William-Dorsch/Open-Source-Train-SIm-Controller-v2/3d files/throttle assembly/throttleHousing.stl

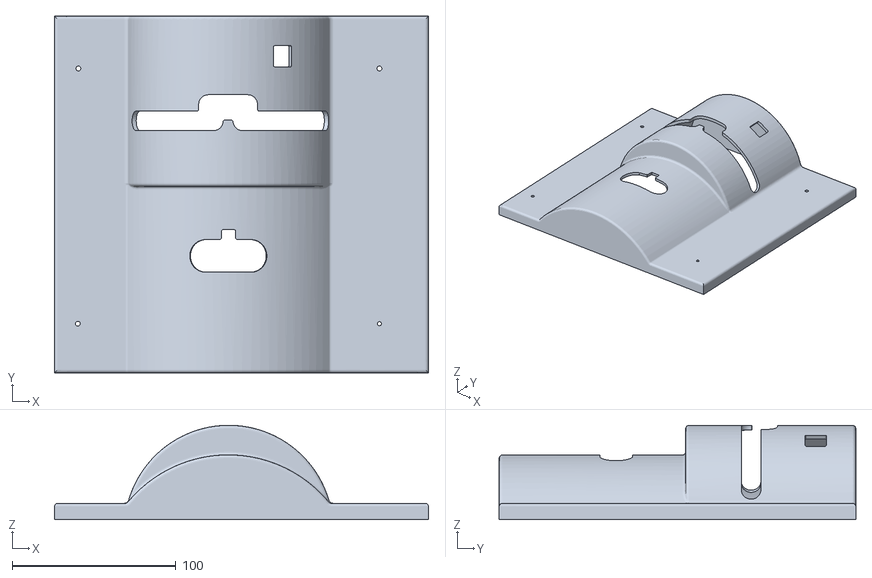
[picture p15: CAD file, 2025-07-15]
3d files/throttle assembly/throttleHousing.stl
228.6 x 218.0 x 57.7
