William-Dorsch/Open-Source-Train-SIm-Controller-v2/3d files/brake assembly/automatic brake/automaticBrakeHandleShaft.stl

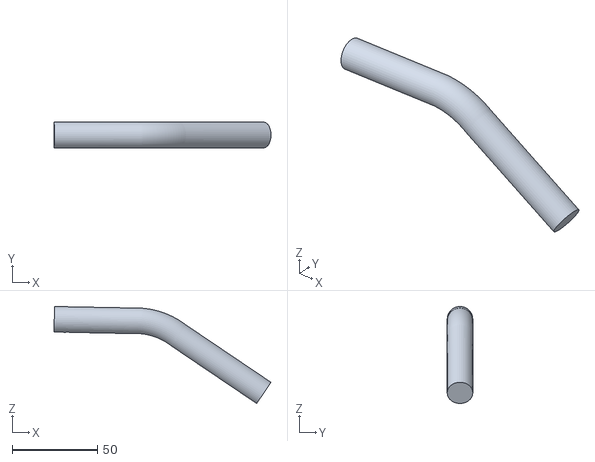
[picture p17: CAD file, 2025-07-15]
3d files/brake assembly/automatic brake/automaticBrakeHandleShaft.stl
127.0 x 15.0 x 56.8
