William-Dorsch/Open-Source-Train-SIm-Controller-v2/3d files/brake assembly/independent brake/independentBrakeHandleShaft.stl

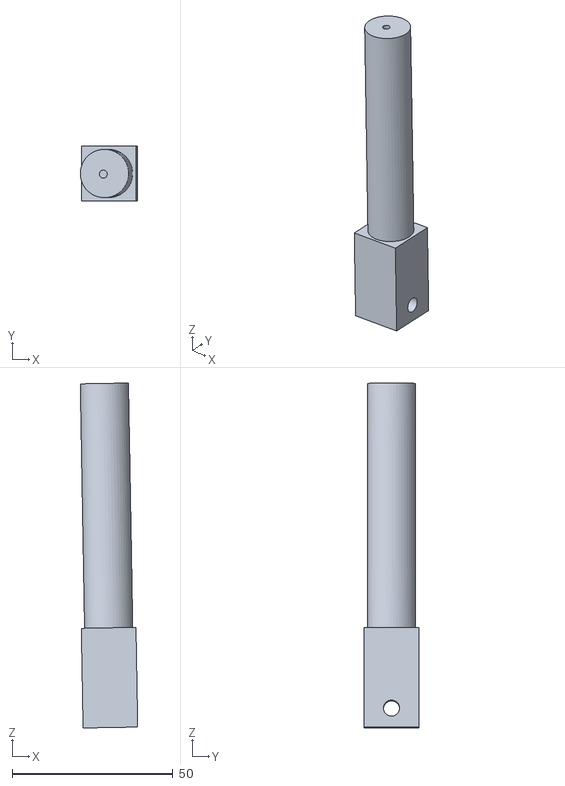
[picture p18: CAD file, 2025-07-15]
3d files/brake assembly/independent brake/independentBrakeHandleShaft.stl
17.9 x 17.0 x 107.3
