William-Dorsch/Open-Source-Train-SIm-Controller-v2/3d files/buttons/hornButtonHousing.stl

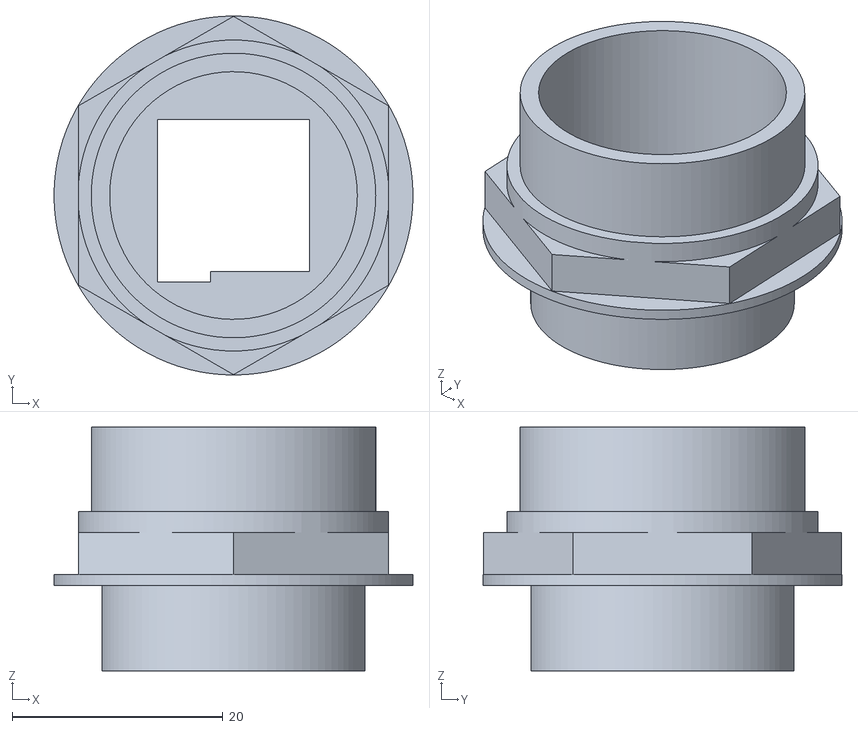
[picture p19: CAD file, 2026-01-03]
3d files/buttons/hornButtonHousing.stl
34.1 x 34.1 x 23.1
