William-Dorsch/Open-Source-Train-SIm-Controller-v2/3d files/throttle assembly/reverser/1x potentiometerHolderShort.stl

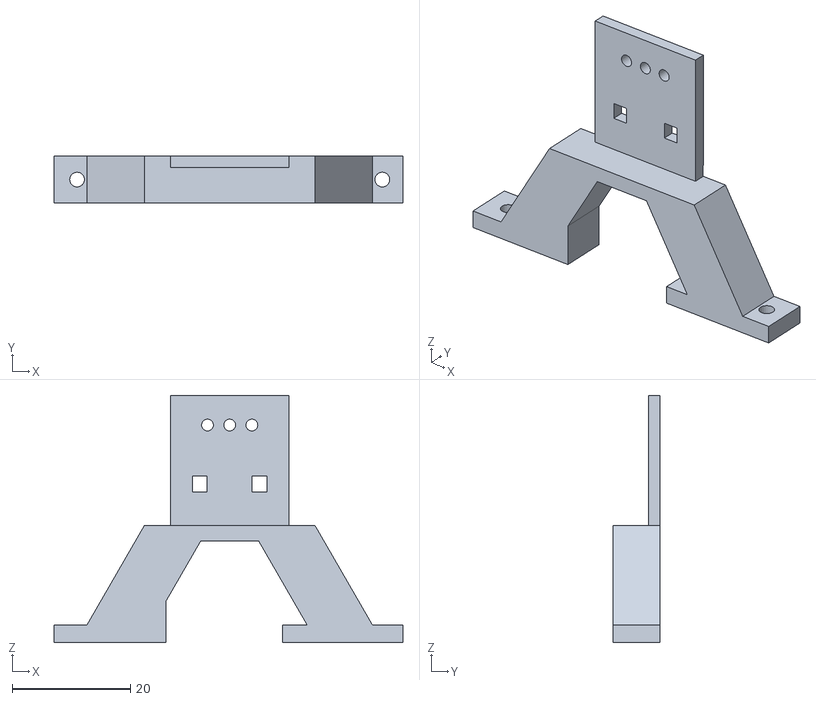
[picture p20: CAD file, 2025-07-15]
3d files/throttle assembly/reverser/1x potentiometerHolderShort.stl
59.0 x 8.00 x 41.8
