William-Dorsch/Open-Source-Train-SIm-Controller-v2/3d files/throttle assembly/throttle/throttleHandle.stl

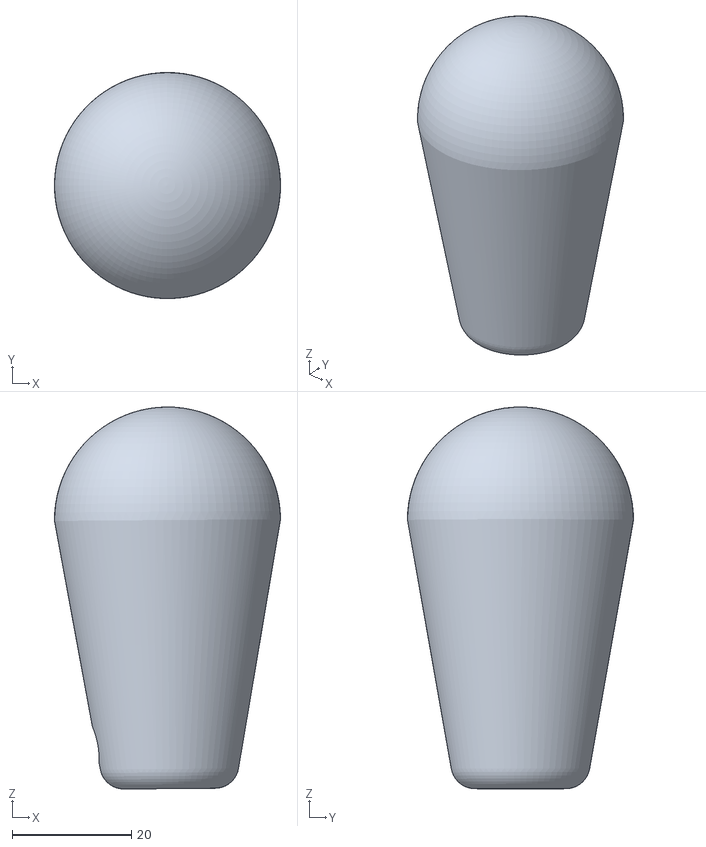
[picture p21: CAD file, 2025-07-15]
3d files/throttle assembly/throttle/throttleHandle.stl
37.9 x 37.9 x 64.0
