William-Dorsch/Open-Source-Train-SIm-Controller-v2/3d files/brake assembly/30A-CDW frame.stl

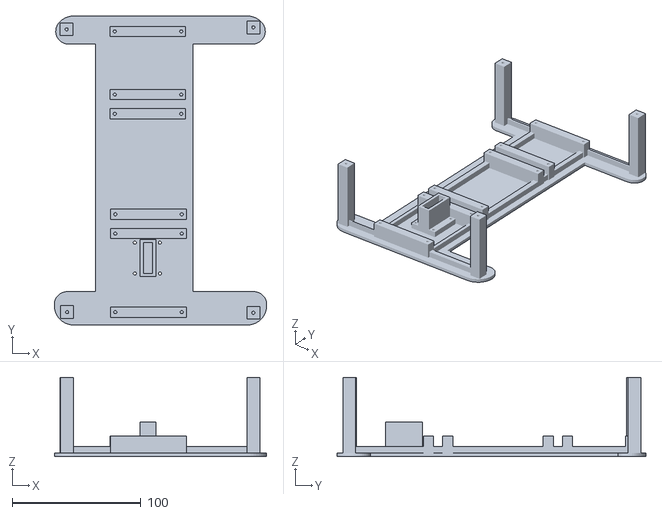
[picture p22: CAD file, 2025-07-15]
3d files/brake assembly/30A-CDW frame.stl
165.0 x 240.0 x 61.7
