William-Dorsch/Open-Source-Train-SIm-Controller-v2/3d files/brake assembly/automatic brake/automaticBrakeAxle.stl

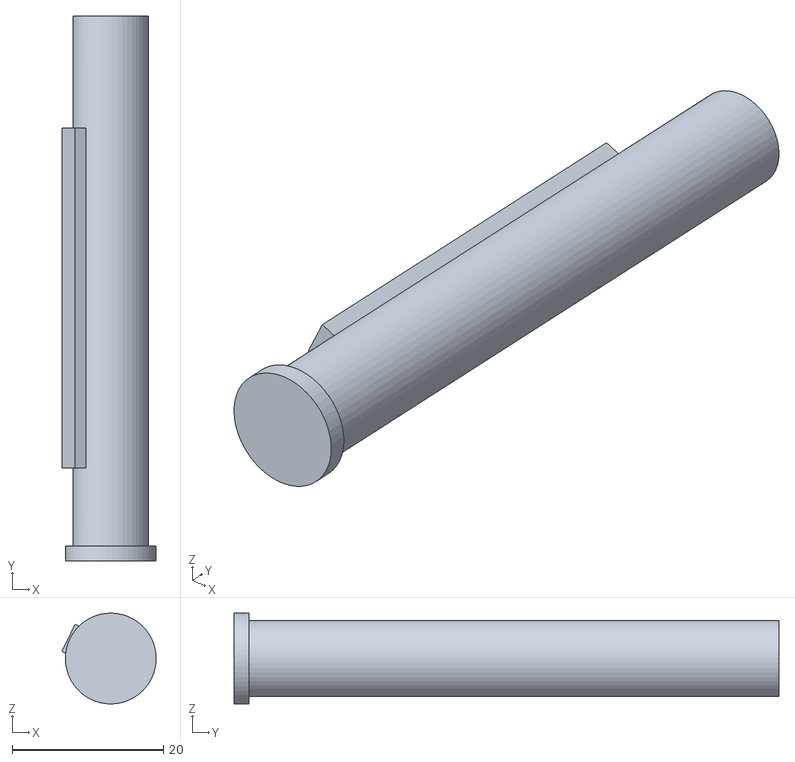
[picture p23: CAD file, 2025-07-15]
3d files/brake assembly/automatic brake/automaticBrakeAxle.stl
12.5 x 72.0 x 12.0
