William-Dorsch/Open-Source-Train-SIm-Controller-v2/3d files/brake assembly/independent brake/independentBrakeAxle.stl

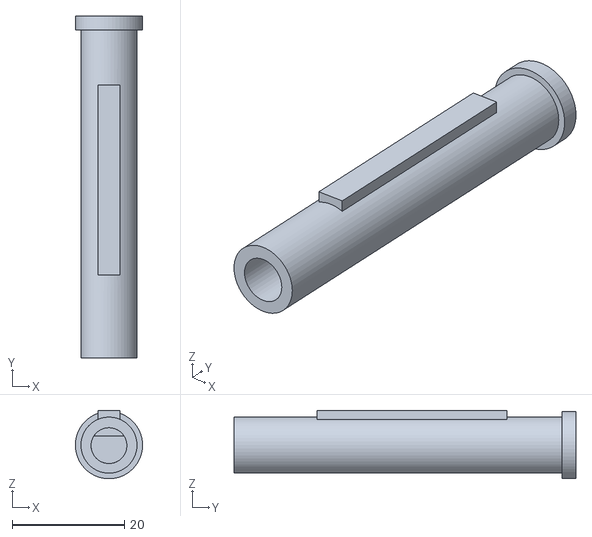
[picture p24: CAD file, 2025-07-15]
3d files/brake assembly/independent brake/independentBrakeAxle.stl
12.0 x 61.0 x 12.2
