William-Dorsch/Open-Source-Train-SIm-Controller-v2/3d files/buttons/sandbutton.stl

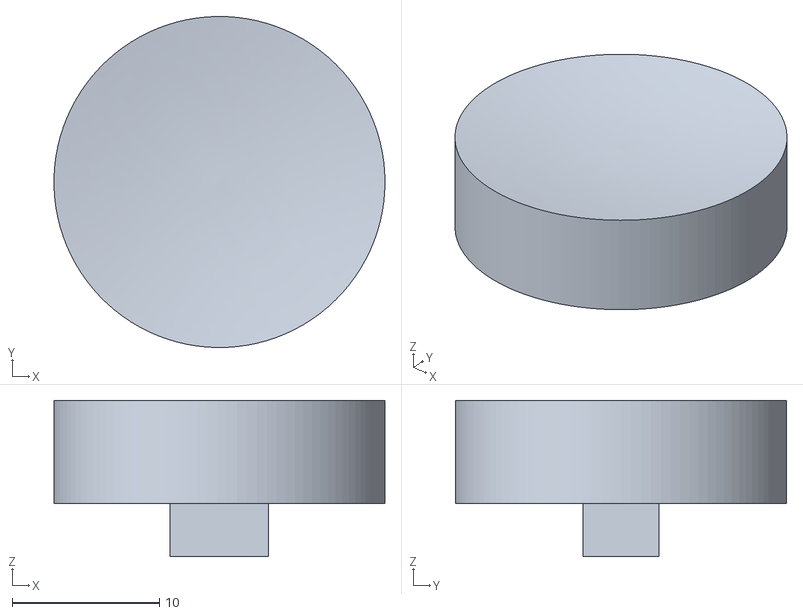
[picture p25: CAD file, 2026-01-03]
3d files/buttons/sandbutton.stl
22.5 x 22.5 x 10.6
