William-Dorsch/Open-Source-Train-SIm-Controller-v2/3d files/throttle assembly/reverser/2x reverserAxleSupport.stl

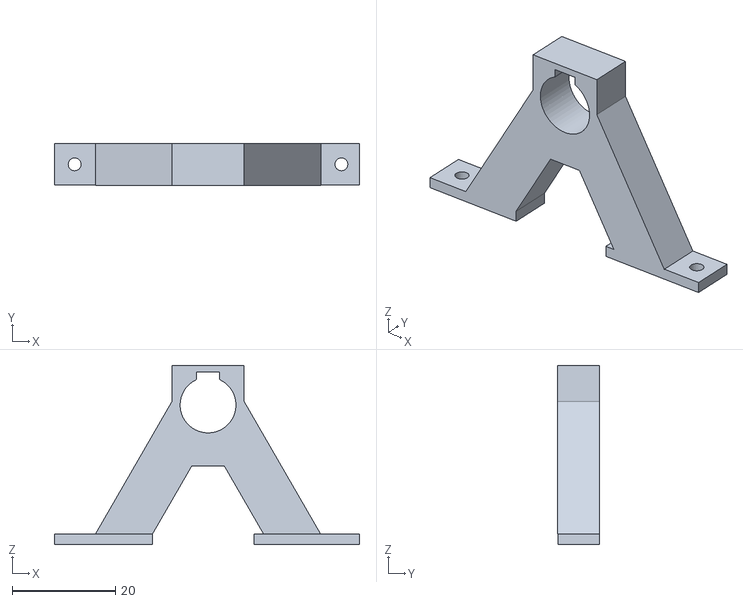
[picture p26: CAD file, 2025-07-15]
3d files/throttle assembly/reverser/2x reverserAxleSupport.stl
59.0 x 8.06 x 34.7
