William-Dorsch/Open-Source-Train-SIm-Controller-v2/3d files/throttle assembly/throttle/notchIndicatorWheel.stl

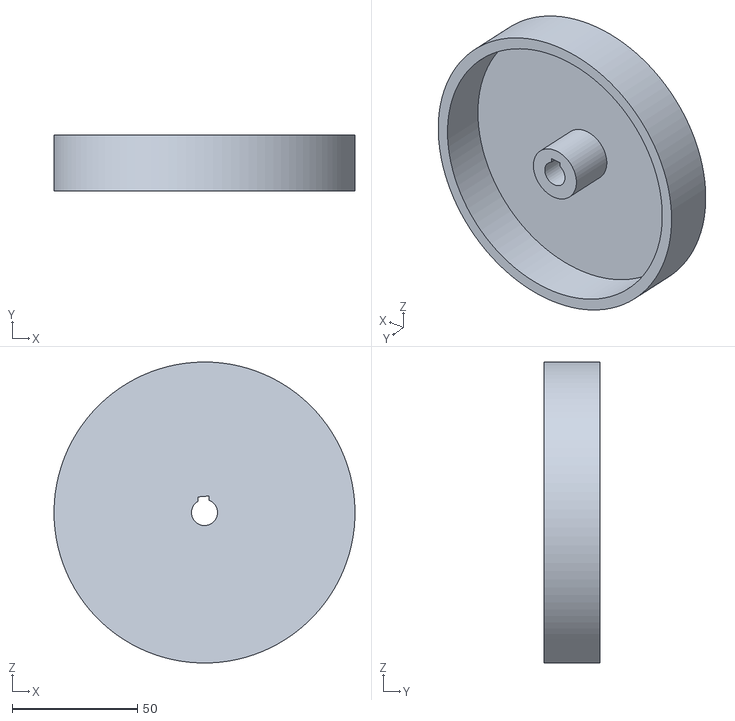
[picture p27: CAD file, 2025-07-15]
3d files/throttle assembly/throttle/notchIndicatorWheel.stl
120.0 x 22.5 x 120.0
