William-Dorsch/Open-Source-Train-SIm-Controller-v2/3d files/brake assembly/automatic brake/automaticBrakeHandle.stl

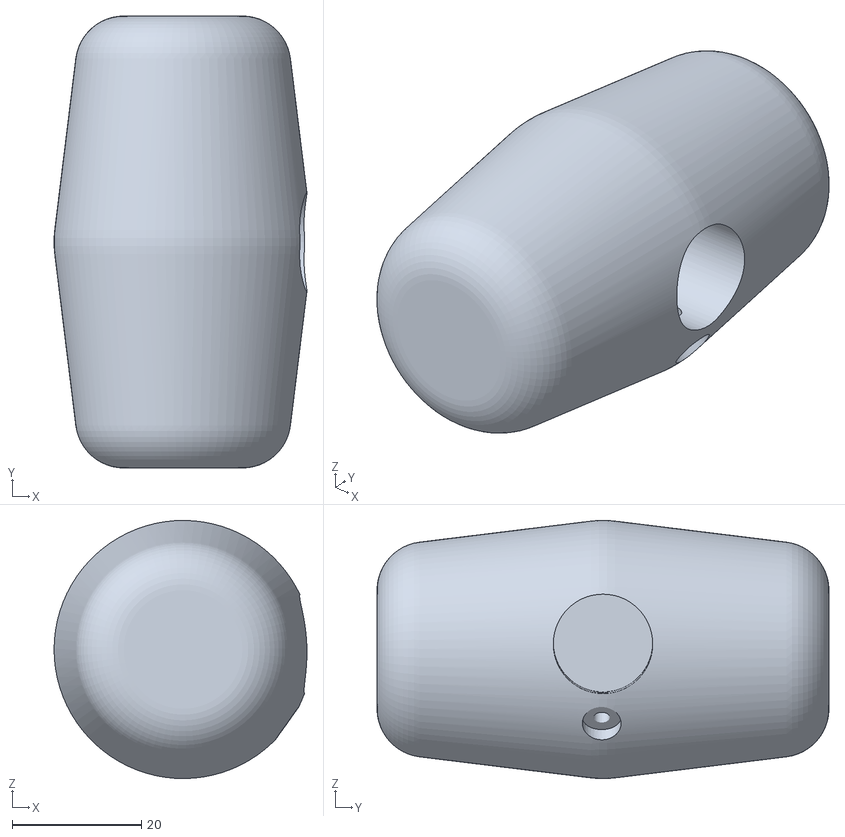
[picture p28: CAD file, 2025-07-15]
3d files/brake assembly/automatic brake/automaticBrakeHandle.stl
39.2 x 70.0 x 40.0
