William-Dorsch/Open-Source-Train-SIm-Controller-v2/3d files/brake assembly/independent brake/independentBrakeWheel.stl

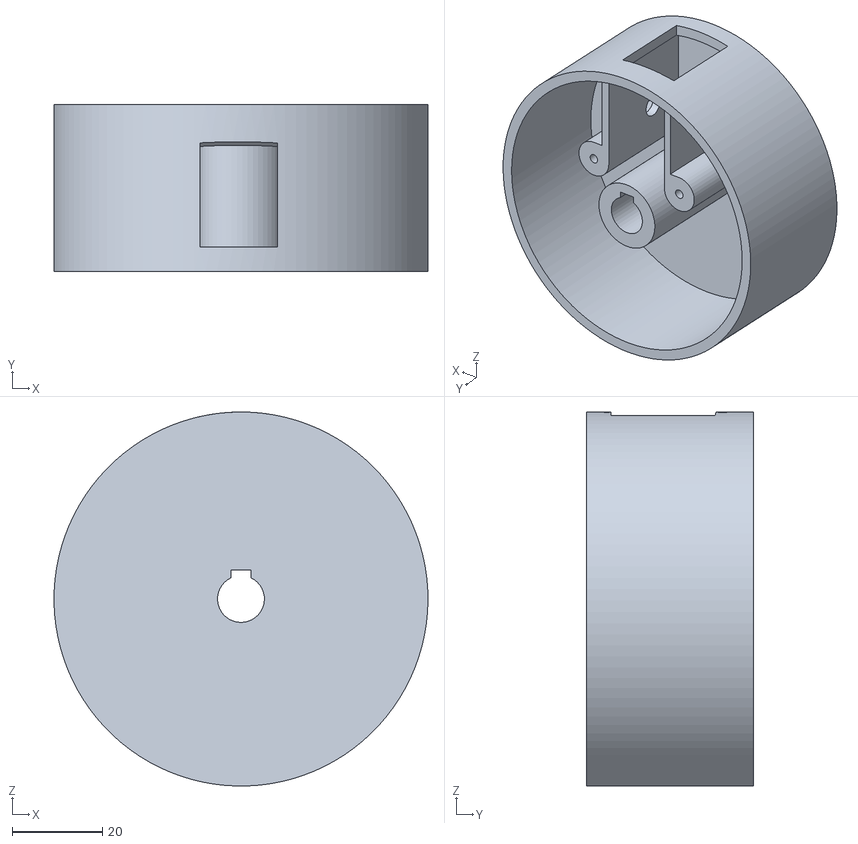
[picture p29: CAD file, 2025-07-15]
3d files/brake assembly/independent brake/independentBrakeWheel.stl
83.0 x 37.0 x 83.0
