William-Dorsch/Open-Source-Train-SIm-Controller-v2/3d files/buttons/hornButton.stl

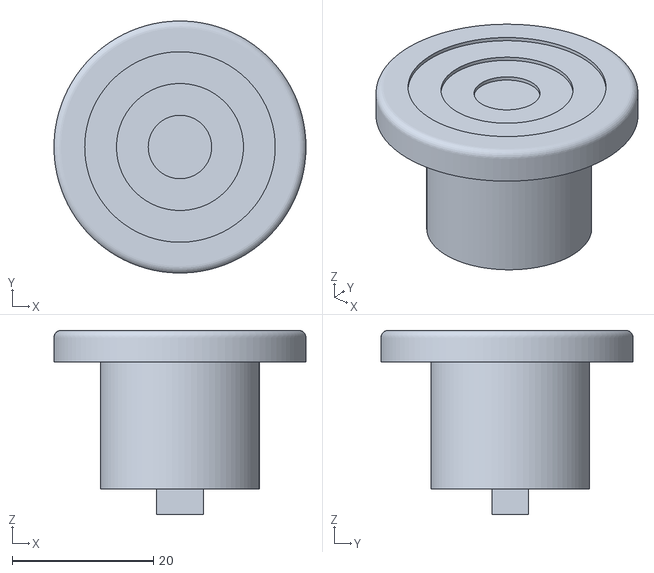
[picture p30: CAD file, 2026-01-03]
3d files/buttons/hornButton.stl
35.7 x 35.7 x 26.1
