William-Dorsch/Open-Source-Train-SIm-Controller-v2/3d files/throttle assembly/throttle/1x axleSupportThin.stl

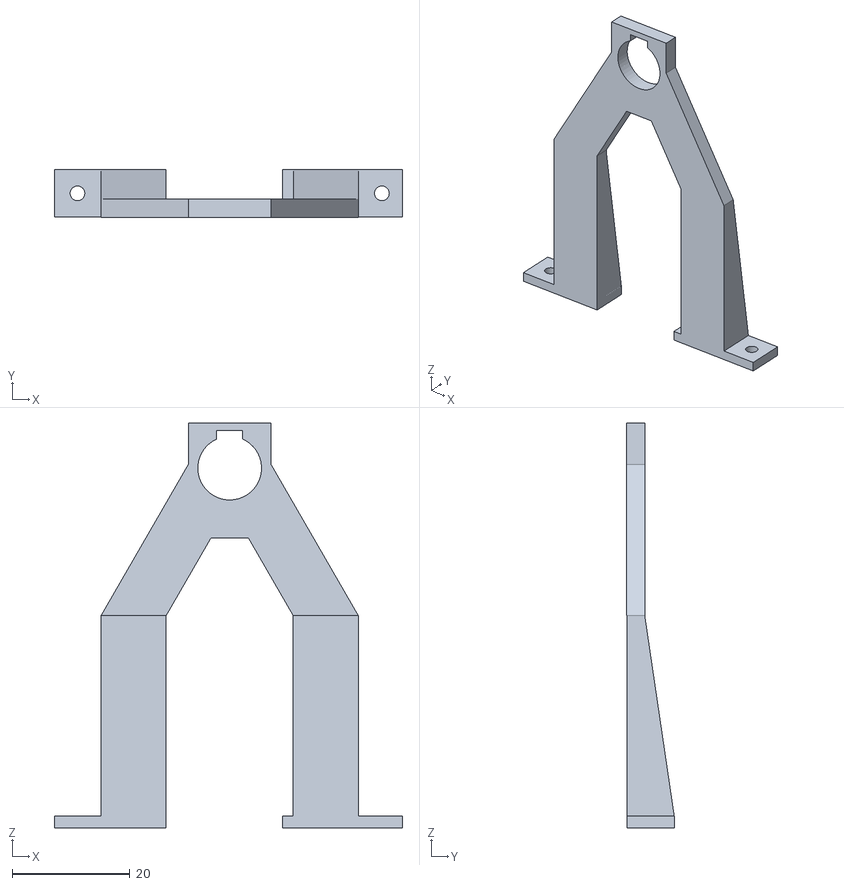
[picture p31: CAD file, 2025-07-15]
3d files/throttle assembly/throttle/1x axleSupportThin.stl
59.0 x 8.06 x 68.7
