William-Dorsch/Open-Source-Train-SIm-Controller-v2/3d files/brake assembly/independent brake/bail off dummy bracket.stl

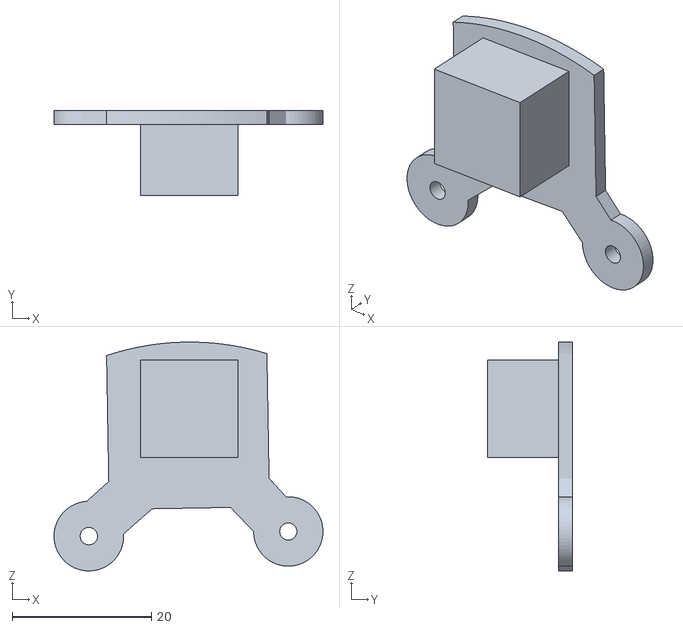
[picture p32: CAD file, 2025-07-15]
3d files/brake assembly/independent brake/bail off dummy bracket.stl
38.6 x 12.2 x 32.8
