William-Dorsch/Open-Source-Train-SIm-Controller-v2/3d files/buttons/leadAxleHousing.stl

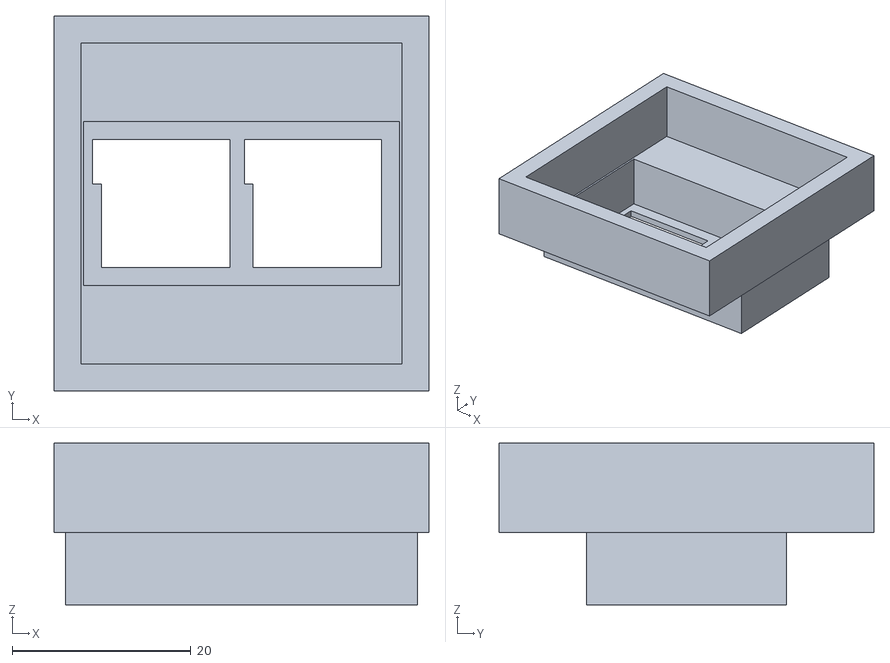
[picture p33: CAD file, 2026-01-03]
3d files/buttons/leadAxleHousing.stl
42.0 x 42.0 x 18.1
