William-Dorsch/Open-Source-Train-SIm-Controller-v2/3d files/throttle assembly/throttle/throttleAxle.stl

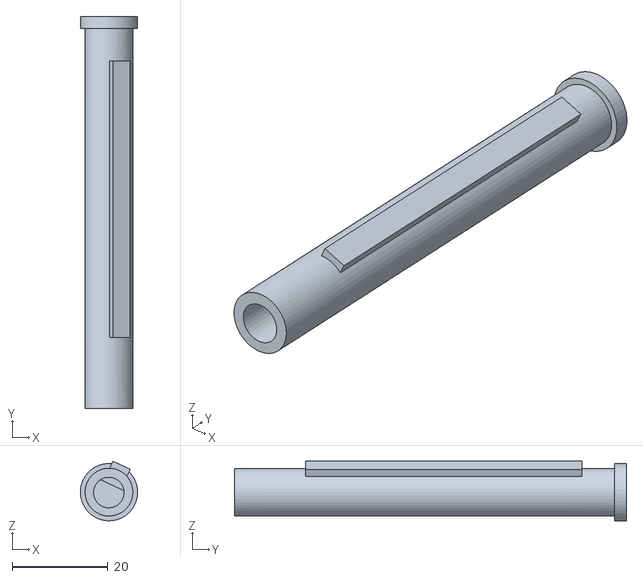
[picture p34: CAD file, 2025-07-15]
3d files/throttle assembly/throttle/throttleAxle.stl
12.0 x 82.0 x 12.5
