William-Dorsch/Open-Source-Train-SIm-Controller-v2/3d files/buttons/sandBase.stl

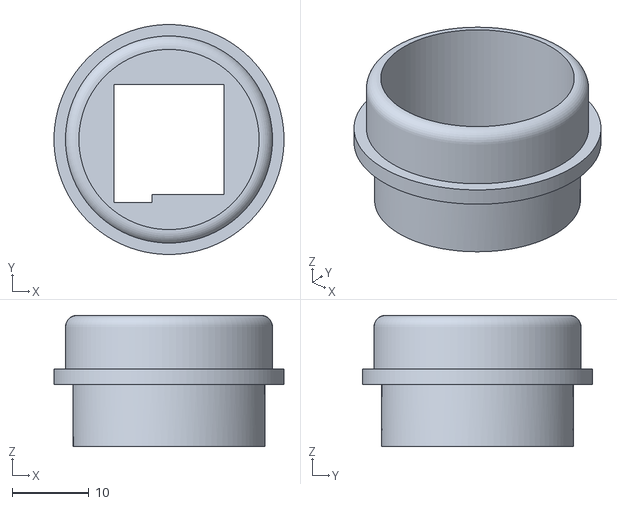
[picture p35: CAD file, 2026-01-03]
3d files/buttons/sandBase.stl
30.0 x 30.0 x 17.1
