William-Dorsch/Open-Source-Train-SIm-Controller-v2/3d files/throttle assembly/throttle/throttleHandleShaft.stl

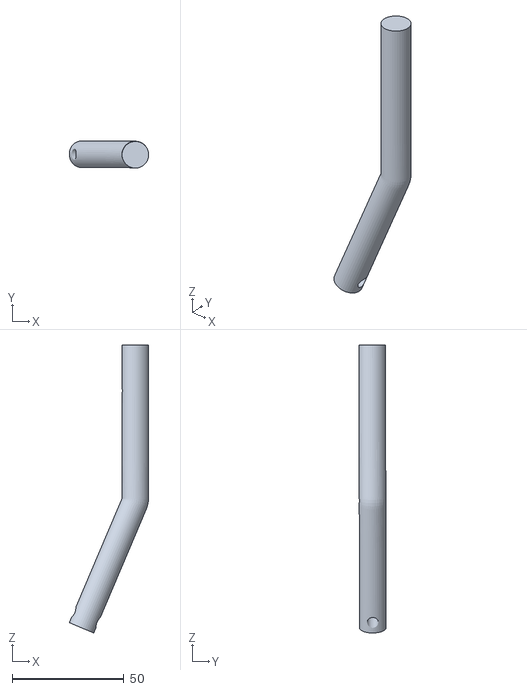
[picture p36: CAD file, 2025-07-15]
3d files/throttle assembly/throttle/throttleHandleShaft.stl
35.5 x 12.1 x 128.7
