William-Dorsch/Open-Source-Train-SIm-Controller-v2/3d files/buttons/leadSandButton.stl

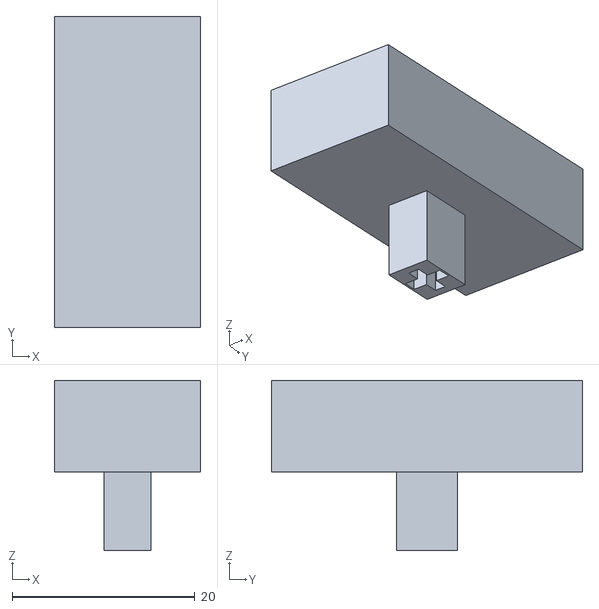
[picture p37: CAD file, 2026-01-03]
3d files/buttons/leadSandButton.stl
16.0 x 34.0 x 18.6
