William-Dorsch/Open-Source-Train-SIm-Controller-v2/3d files/throttle assembly/throttle/throttleWheel.stl

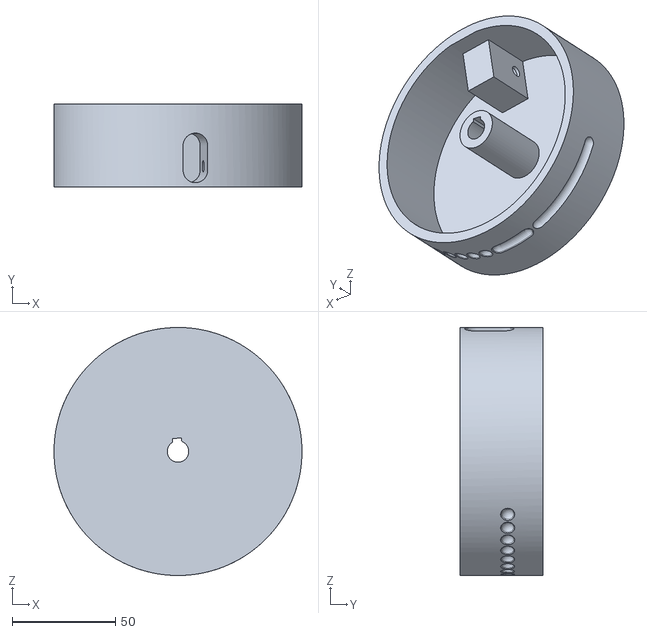
[picture p38: CAD file, 2025-07-15]
3d files/throttle assembly/throttle/throttleWheel.stl
120.0 x 40.0 x 120.0
