William-Dorsch/Open-Source-Train-SIm-Controller-v2/3d files/buttons/bellButton.stl

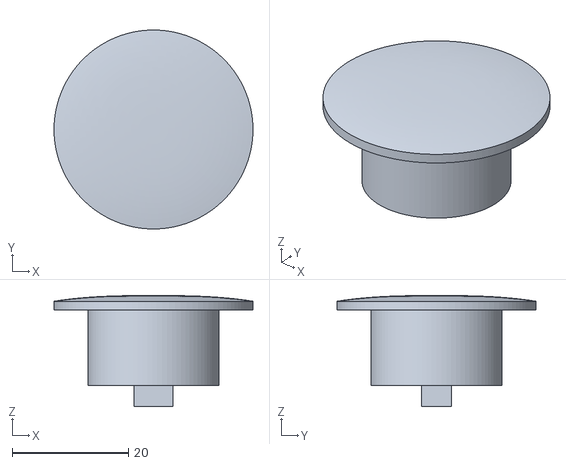
[picture p39: CAD file, 2026-01-03]
3d files/buttons/bellButton.stl
34.2 x 34.2 x 19.1
